kholia/Global-Communications-Transceiver/screenshots/3D-Render.png

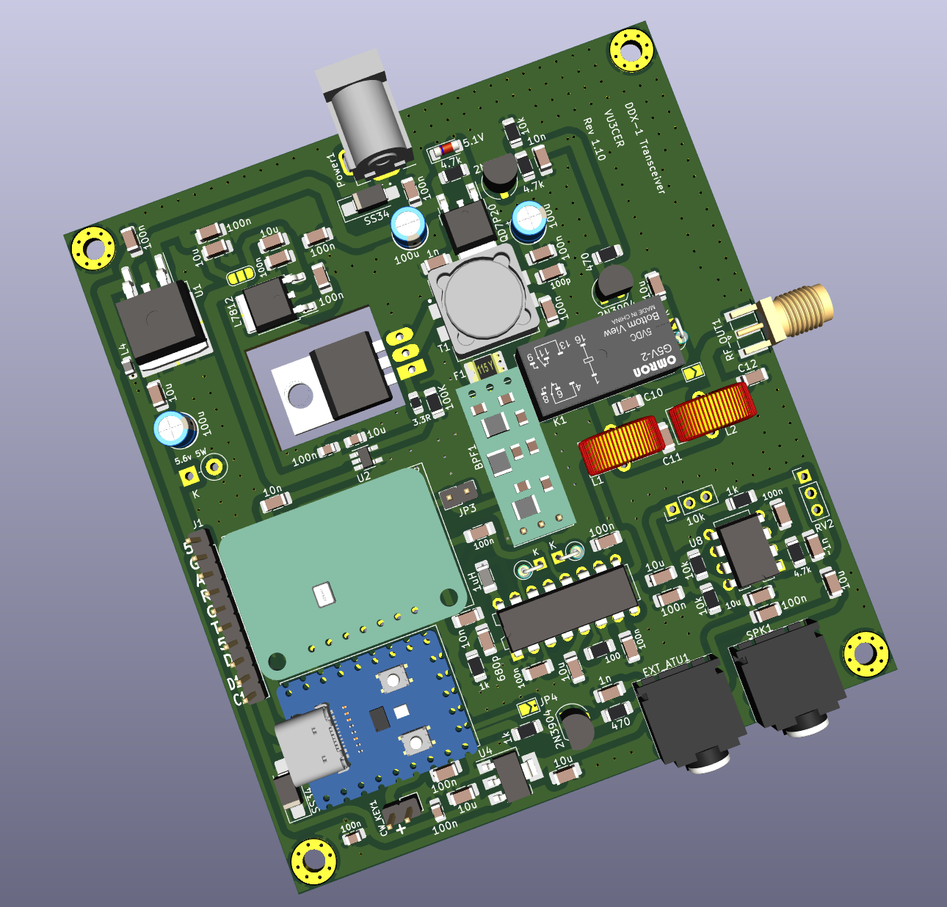
screenshots/3D-Render.png
