kholia/Global-Communications-Transceiver/screenshots/Canada-RX-Screenshot_2024-01-10_13-42-16.png

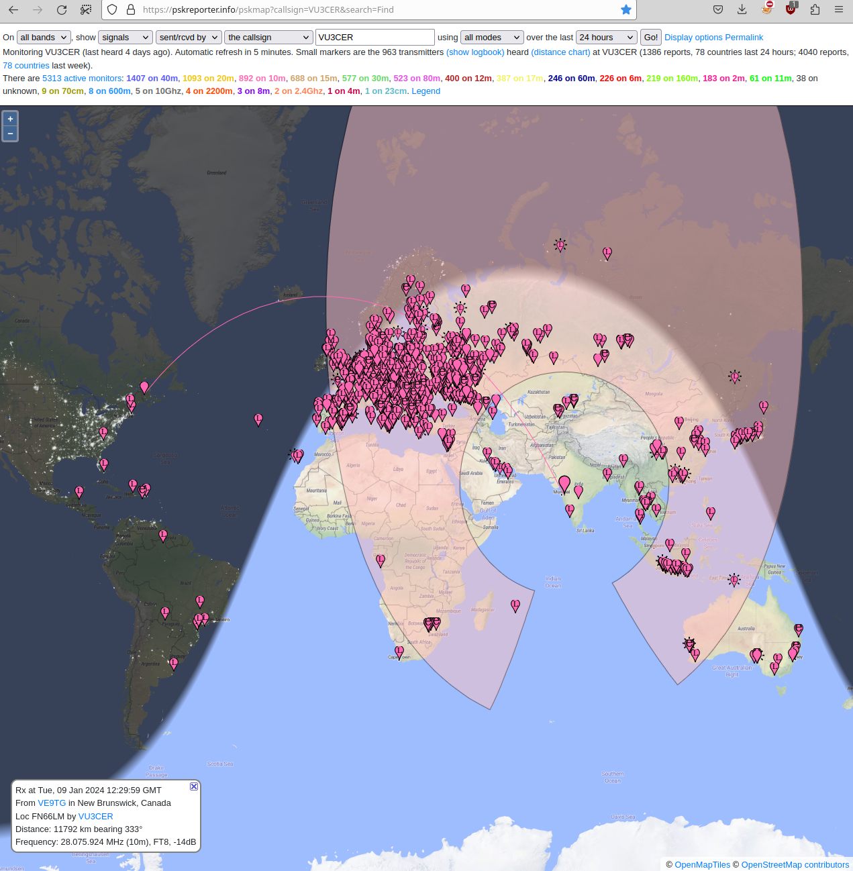
screenshots/Canada-RX-Screenshot_2024-01-10_13-42-16.png
