kholia/Global-Communications-Transceiver/screenshots/CD2003 + Pro-BPF - Screenshot_2023-11-12_18-27-18.png

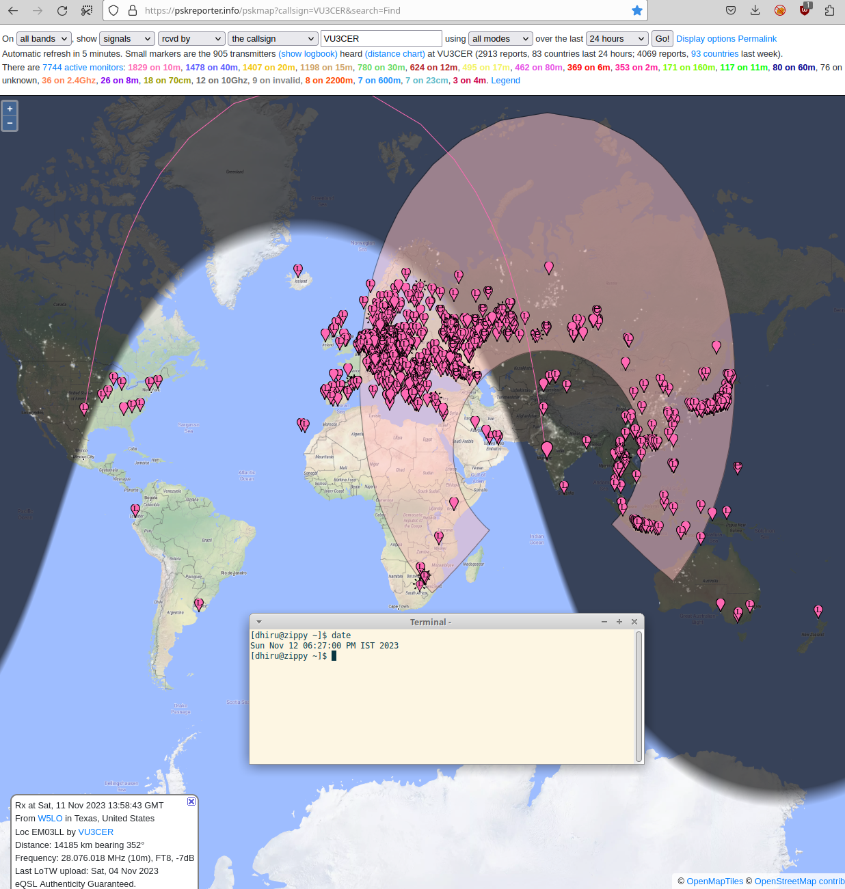
screenshots/CD2003 + Pro-BPF - Screenshot_2023-11-12_18-27-18.png
