kholia/Global-Communications-Transceiver/screenshots/DDX-"Breadboard"-Screenshot_2023-11-18_21-17-12.png

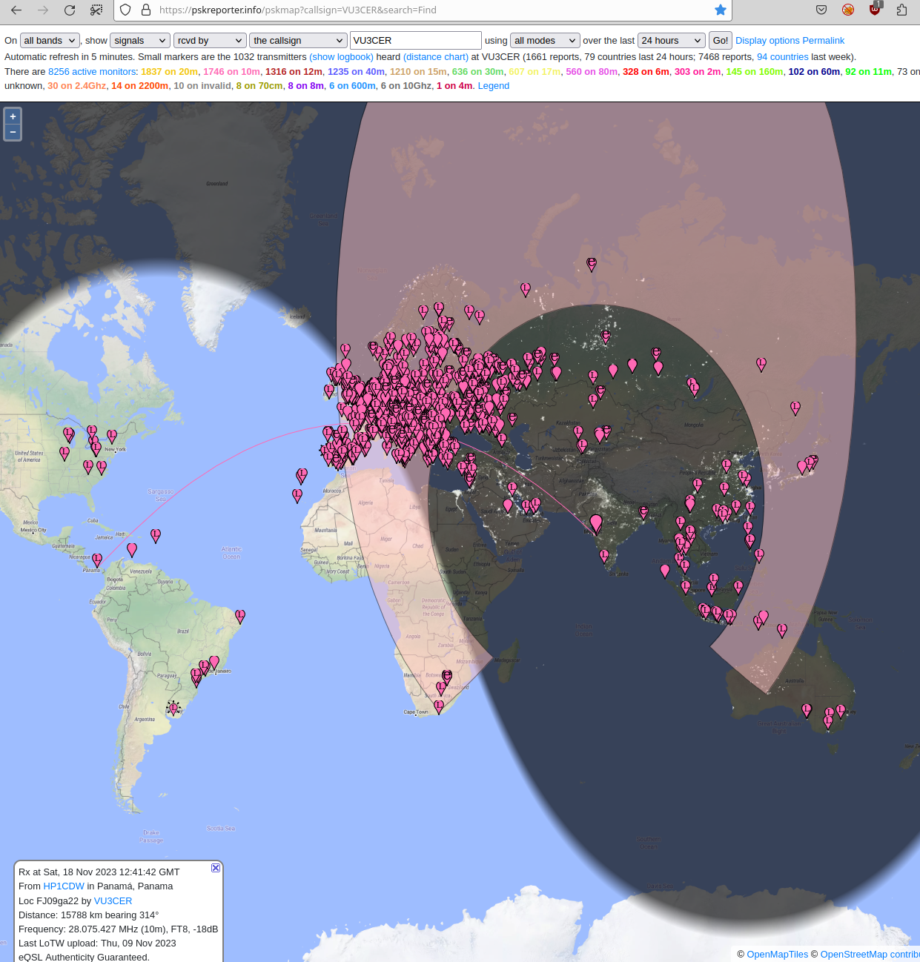
screenshots/DDX-"Breadboard"-Screenshot_2023-11-18_21-17-12.png
