kholia/Global-Communications-Transceiver/screenshots/DDX-"Breadboard"-Screenshot_2023-11-19_18-49-43.png

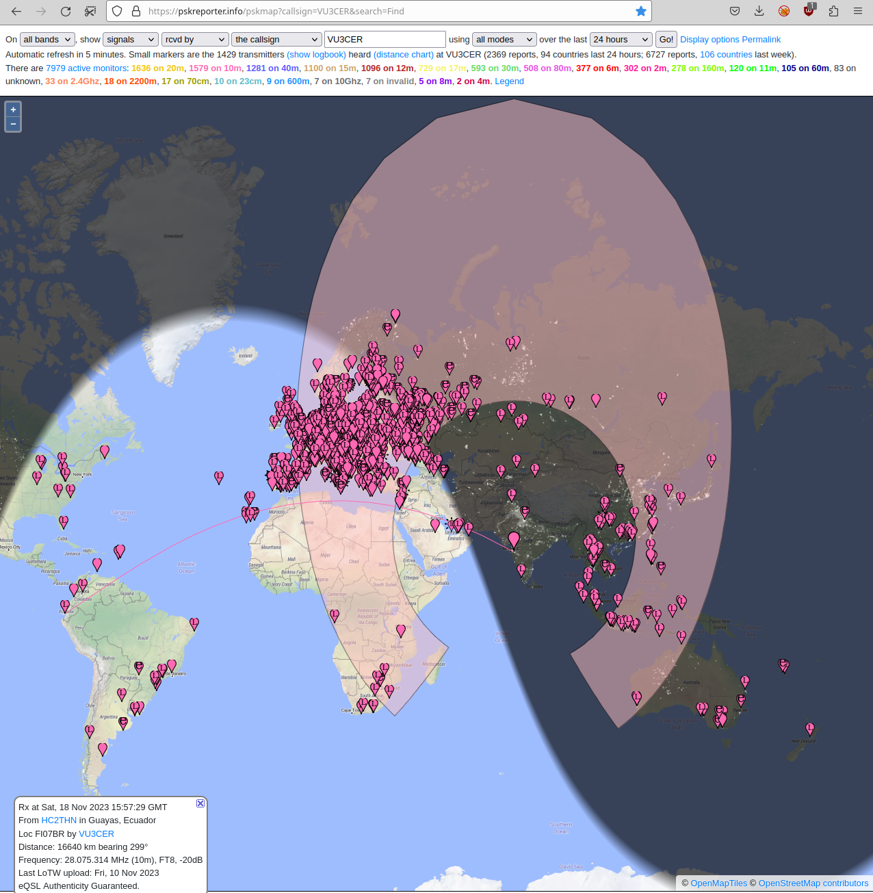
screenshots/DDX-"Breadboard"-Screenshot_2023-11-19_18-49-43.png
