kholia/Global-Communications-Transceiver/screenshots/DDX-SMD-BPF-Screenshot_2024-01-23_20-59-59.png

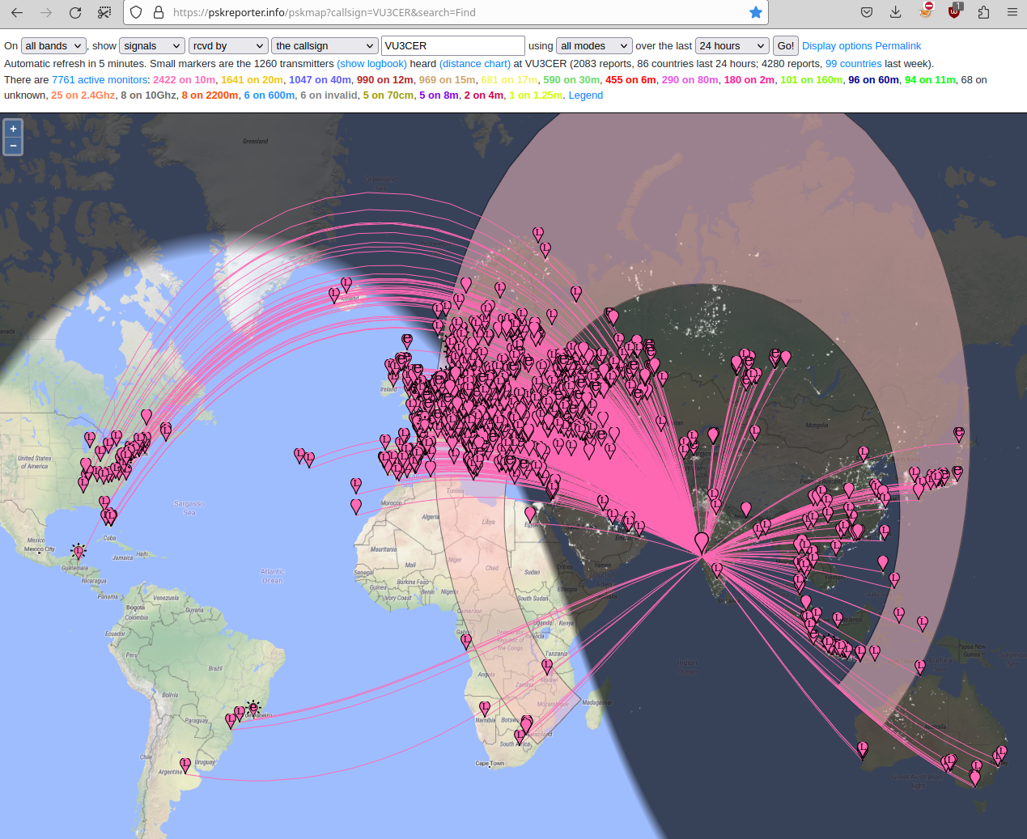
screenshots/DDX-SMD-BPF-Screenshot_2024-01-23_20-59-59.png
