kholia/Global-Communications-Transceiver/screenshots/Pico-ADC-Screenshot_2023-11-22_10-23-36.png

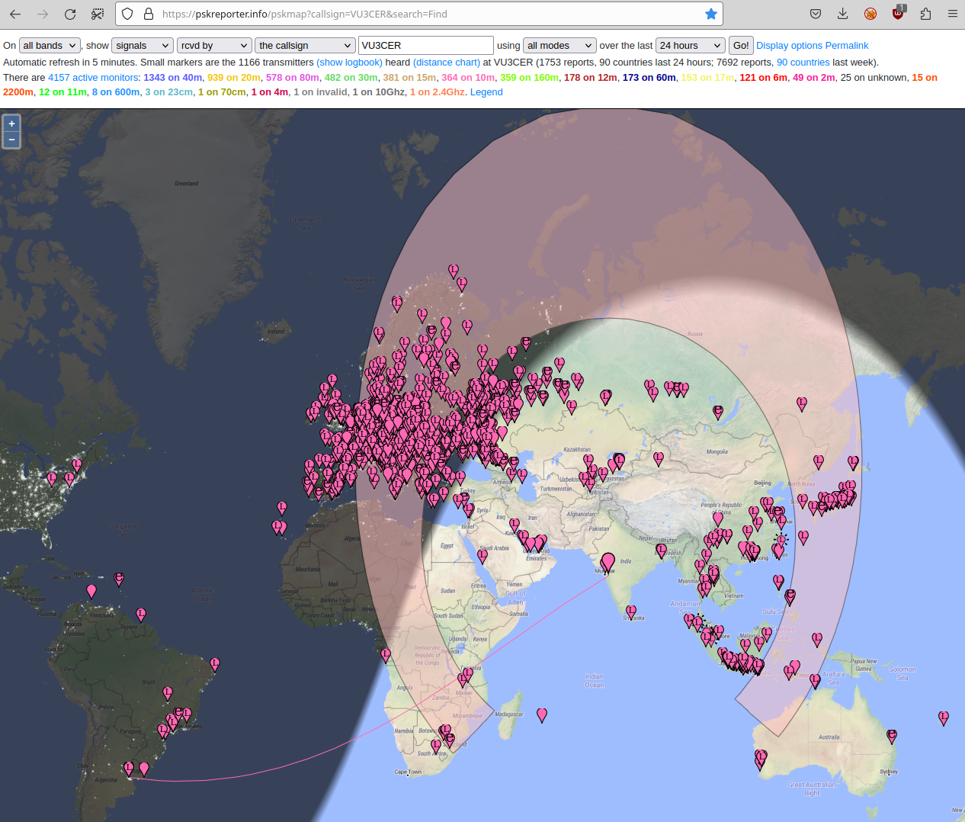
screenshots/Pico-ADC-Screenshot_2023-11-22_10-23-36.png
