kholia/Global-Communications-Transceiver/screenshots/Pico-ADC-Screenshot_2023-11-22_13-47-27.png

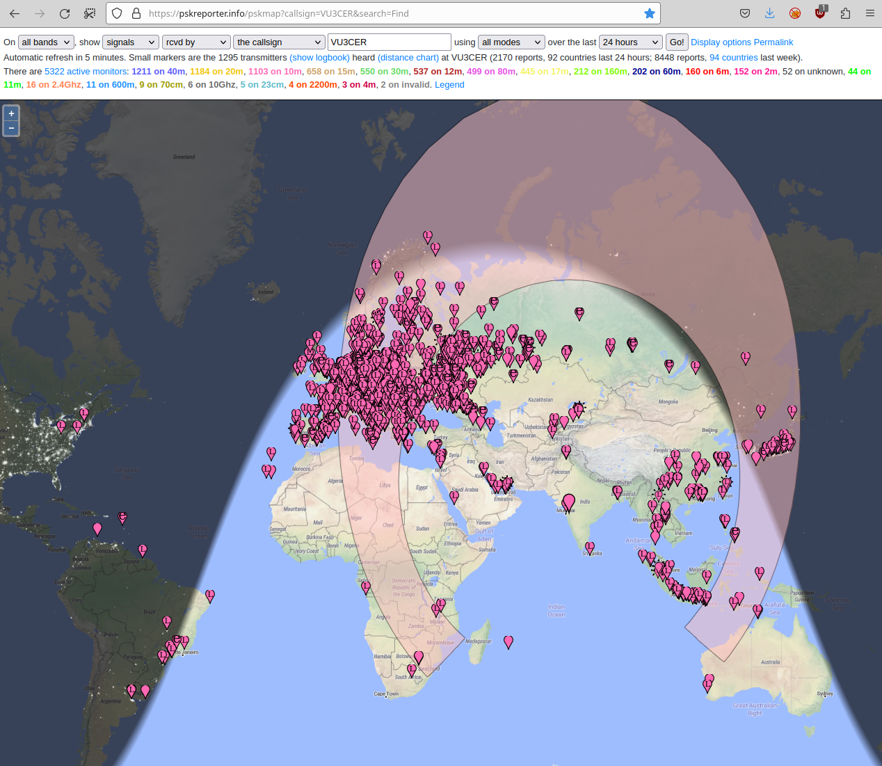
screenshots/Pico-ADC-Screenshot_2023-11-22_13-47-27.png
