kholia/Global-Communications-Transceiver/screenshots/RX-Screenshot_2023-11-30_21-45-04.png

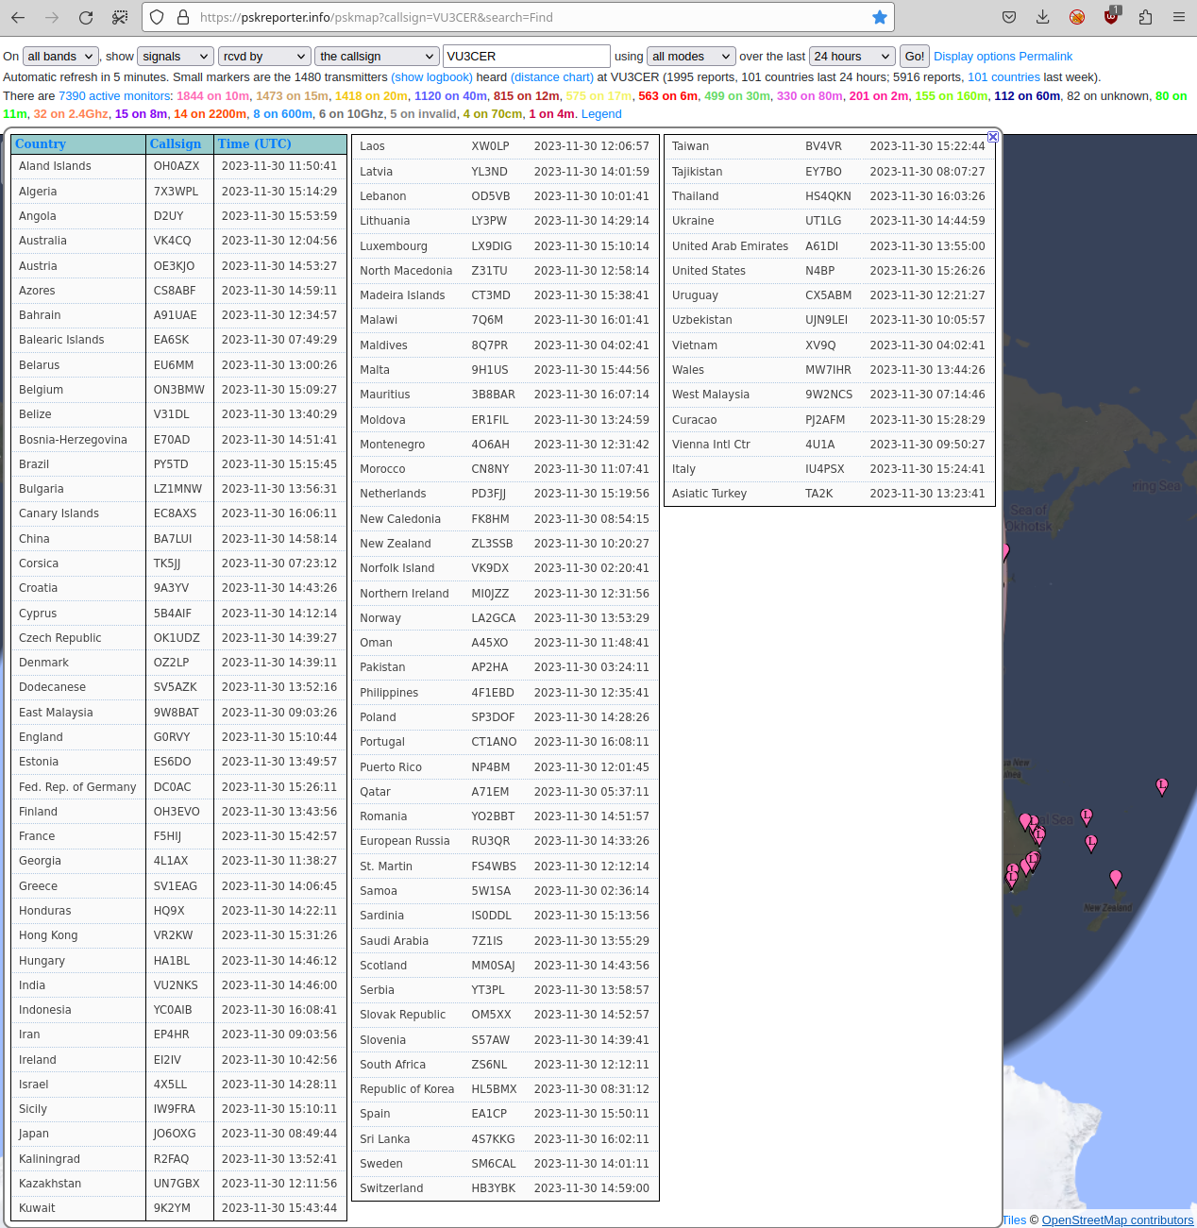
screenshots/RX-Screenshot_2023-11-30_21-45-04.png
