kholia/Global-Communications-Transceiver/screenshots/RX-Screenshot_2024-01-05_20-14-19.png

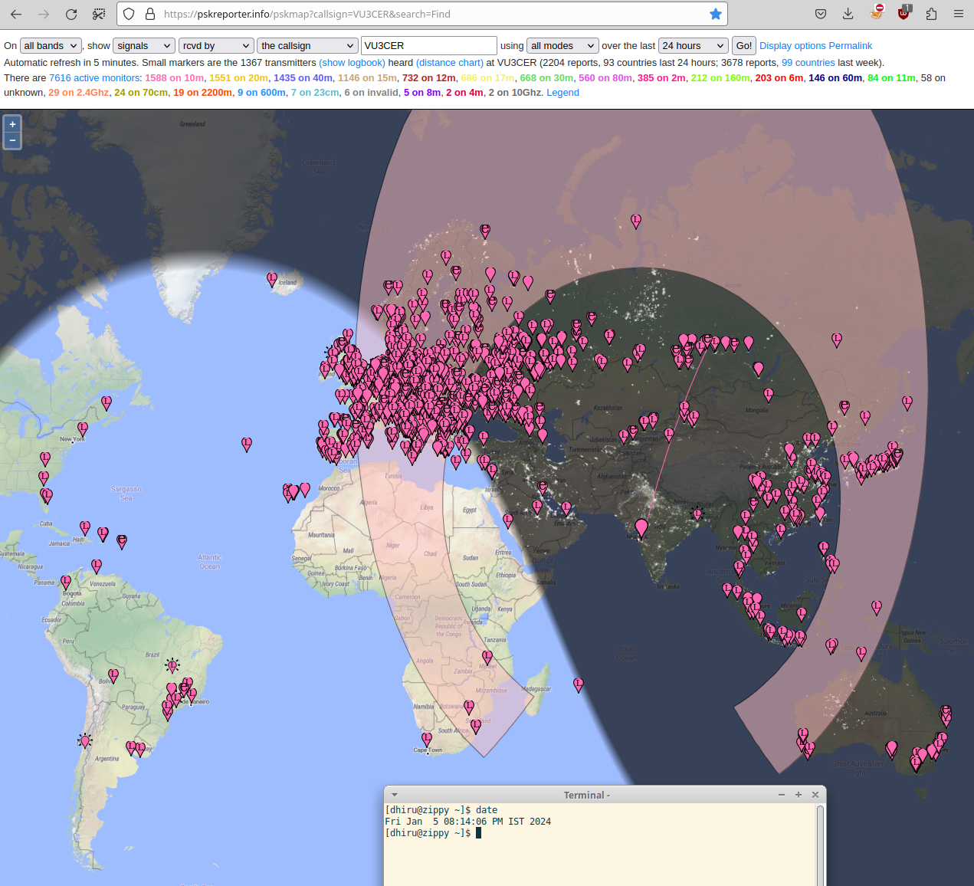
screenshots/RX-Screenshot_2024-01-05_20-14-19.png
