kholia/Global-Communications-Transceiver/screenshots/Screenshot_2023-11-12_19-14-23.png

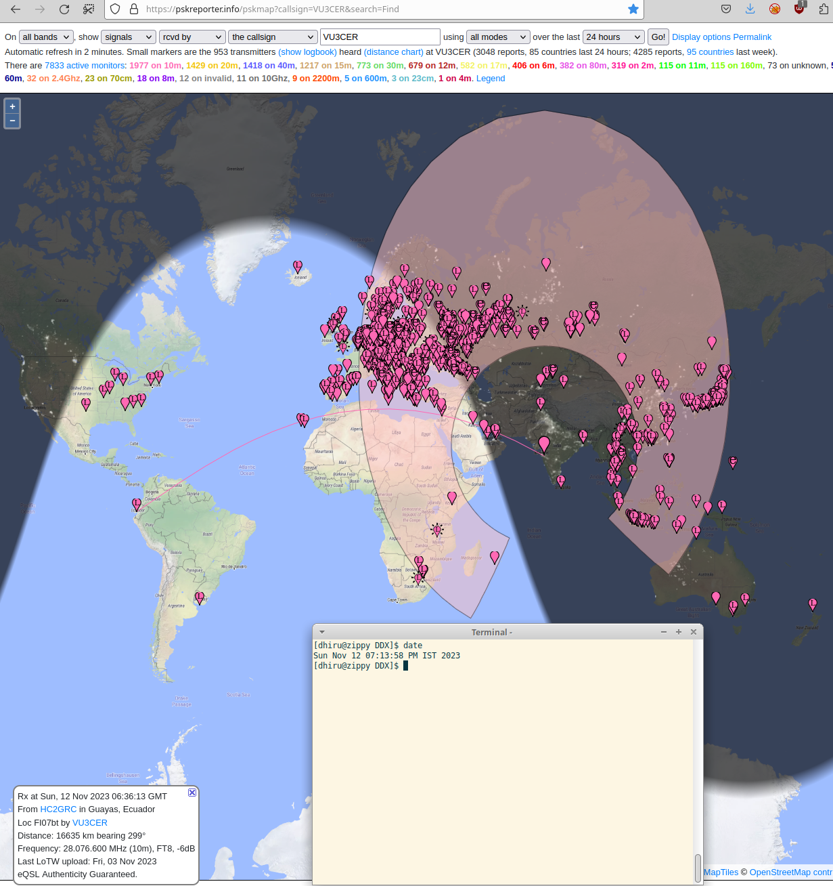
screenshots/Screenshot_2023-11-12_19-14-23.png
