kholia/Global-Communications-Transceiver/screenshots/Screenshot_2023-11-17_19-35-54.png

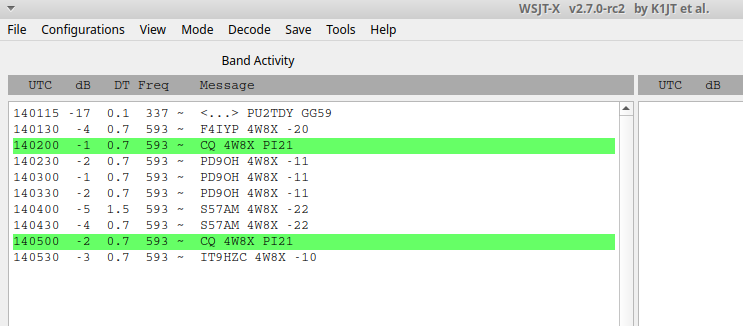
screenshots/Screenshot_2023-11-17_19-35-54.png
