kholia/Global-Communications-Transceiver/screenshots/US-Screenshot_2023-11-30_19-38-38.png

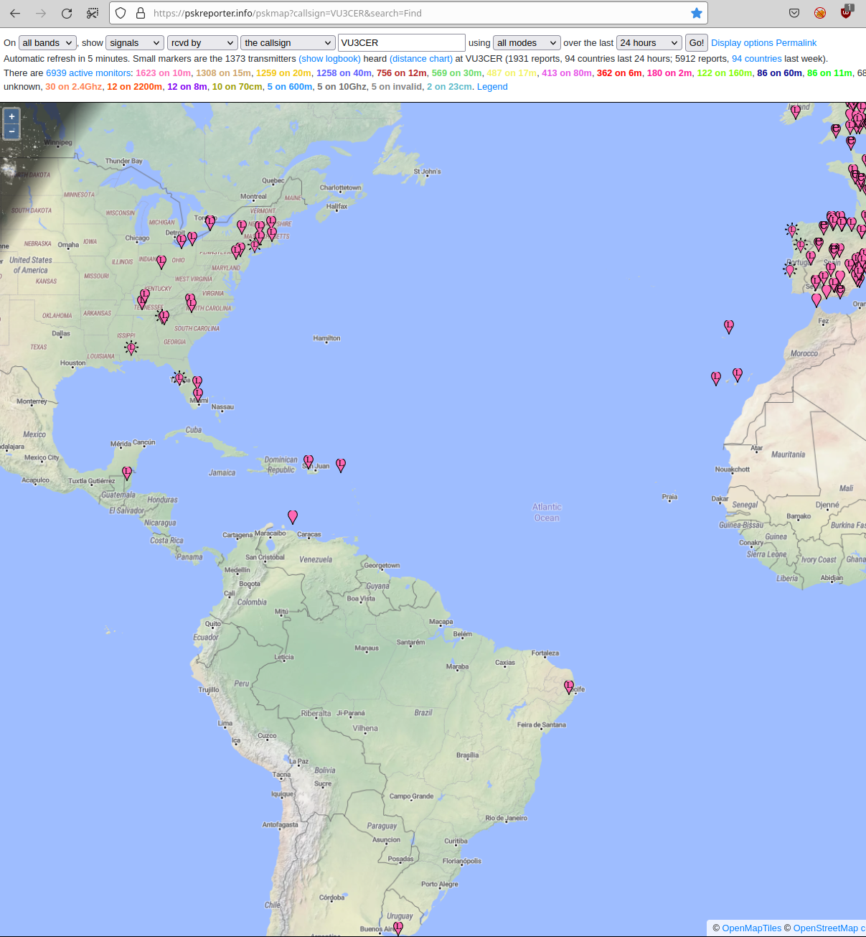
screenshots/US-Screenshot_2023-11-30_19-38-38.png
