kholia/Global-Communications-Transceiver/wsjtx_helper/Screenshot_2022-12-24_08-32-39.png

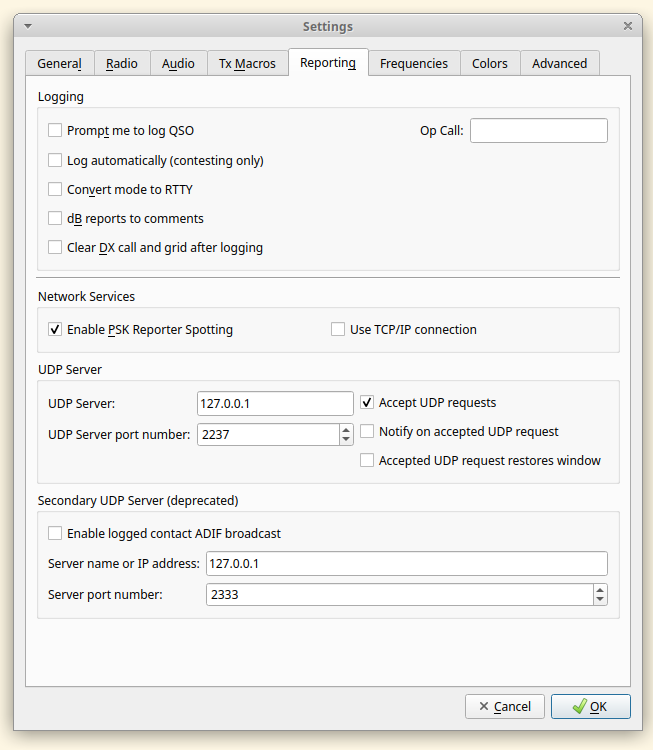
wsjtx_helper/Screenshot_2022-12-24_08-32-39.png
