kholia/Global-Communications-Transceiver/design-files/audioamp.asc

C1: cap; 10nF
C2: cap; 1µF
C: cap; 10µ
R2: res; 10k
R3: res; 10k
Rf1: res; 1k
Rf2: res; 4.7k
U2: MCP6002
V2: VOLTAGE; 3.3
V3: voltage; SINE(0 0.3 200)
V4: VOLTAGE; 3.3
Named nets: 0, IN
.tran 1s
.options maxstep=10u
.fourier 1K V(a)
